mattdibi/yampad/img/acrylic_case/yampad (3 of 10).jpg

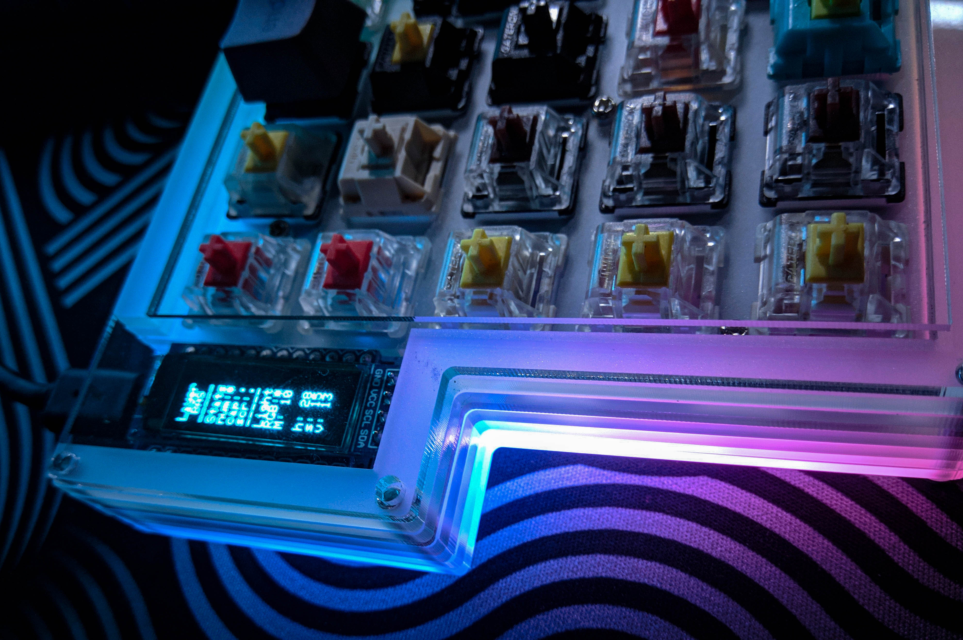
img/acrylic_case/yampad (3 of 10).jpg
