mattdibi/yampad/img/acrylic_case/yampad (5 of 10).jpg

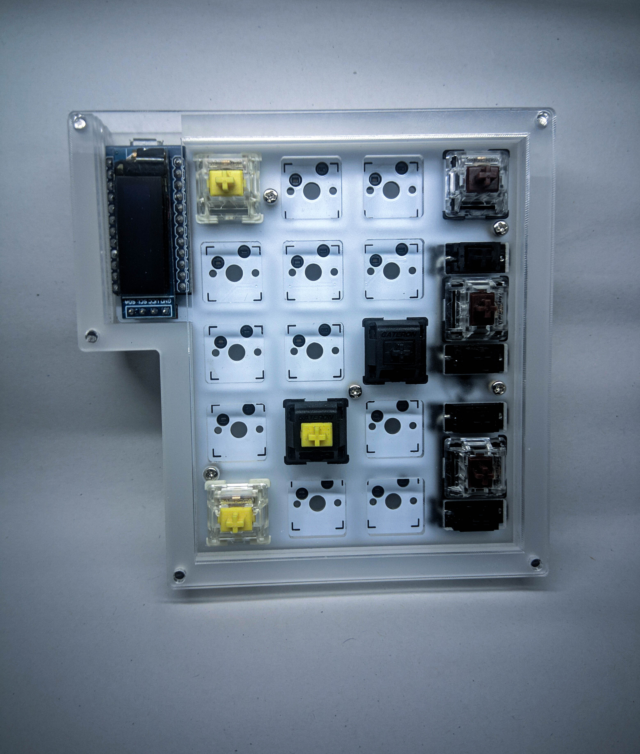
img/acrylic_case/yampad (5 of 10).jpg
