mattdibi/yampad/img/acrylic_case/yampad (6 of 10).jpg

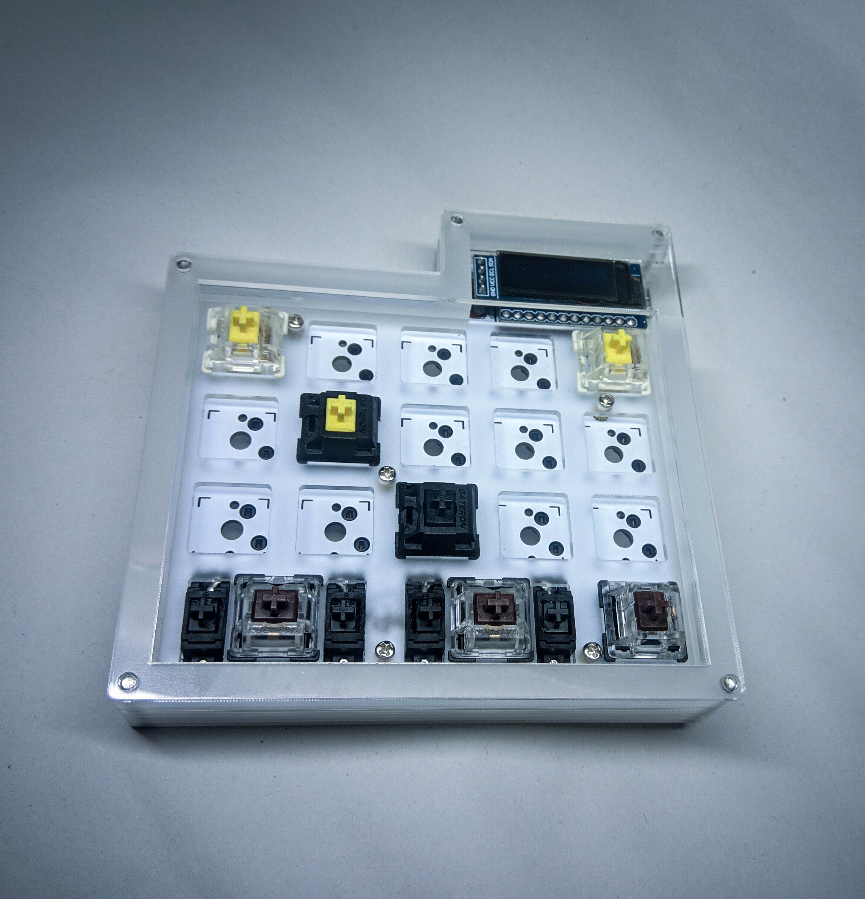
img/acrylic_case/yampad (6 of 10).jpg
