mattdibi/yampad/img/acrylic_case/yampad (7 of 10).jpg

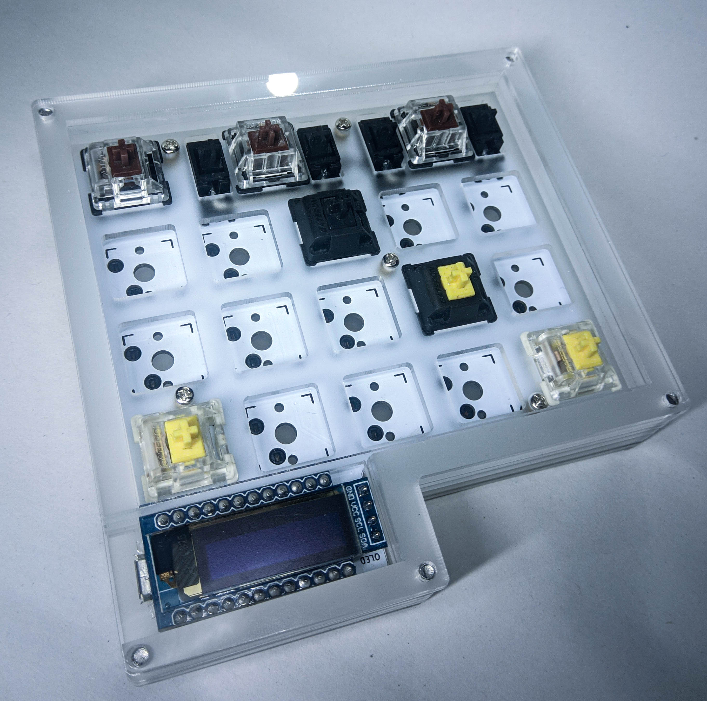
img/acrylic_case/yampad (7 of 10).jpg
